CryptoIceMLH/ImmergeAxe/Wiring Diagram/immergeaxe.kicad_sch

## KiCad design Wiring Diagram/immergeaxe.kicad_sch (2025-02-03)

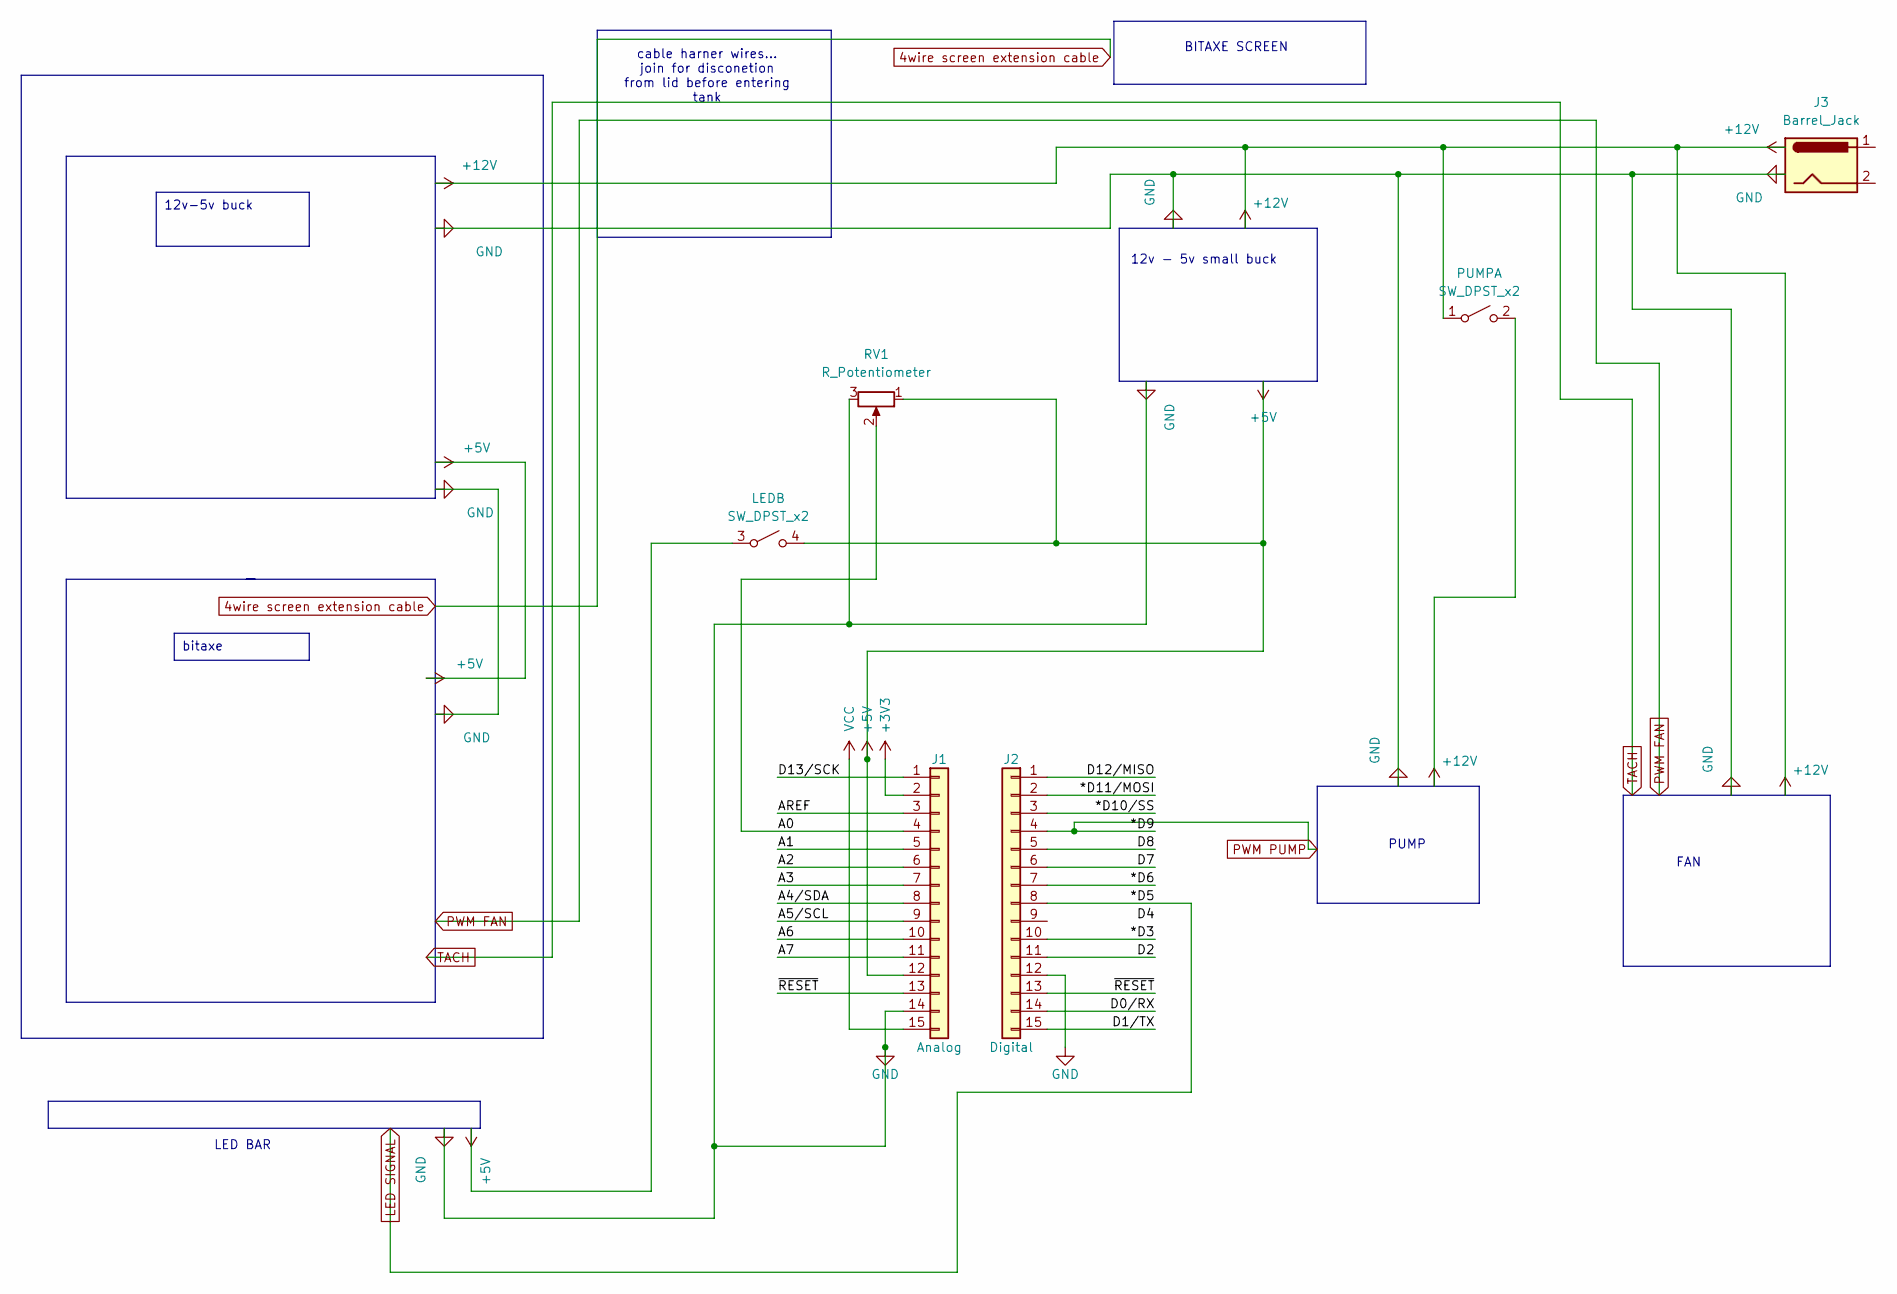
[picture p14: schematic immergeaxe.kicad_sch]

Parts:
J1: Analog; PinHeader_1x15_P2.54mm_Vertical
J2: Digital; PinHeader_1x15_P2.54mm_Vertical
J3: Barrel_Jack
LED: SW_DPST_x2
PUMP: SW_DPST_x2
RV1: R_Potentiometer

Connections:
+3V3: J1.2
+5V: J1.12, LED.3 (A), LED.4 (B), RV1.1
+12V: PUMP.1 (A), PUMP.2 (B)
A0: J1.4, RV1.2
A1: J1.5
A2: J1.6
A3: J1.7
A4/SDA: J1.8
A5/SCL: J1.9
A6: J1.10
A7: J1.11
AREF: J1.3
D0/RX: J2.14
D1/TX: J2.15
D2: J2.11
D7: J2.6
D8: J2.5
D12/MISO: J2.1
D13/SCK: J1.1
GND: J1.14, J2.12, RV1.3
VCC: J1.15
d3: J2.10
d5: J2.8
d6: J2.7
d9: J2.4
d10/ss: J2.3
d11/mosi: J2.2
~RESET: J1.13, J2.13

Notes on the sheet:
12v-5v buck
PUMP
bitaxe
FAN
cable harner wires... join for disconetion from lid before entering tank
LED BAR
12v - 5v small buck
BITAXE SCREEN
